rolohaun/SimpleCore/Mantis_Toolhead/Left_Duct.stl

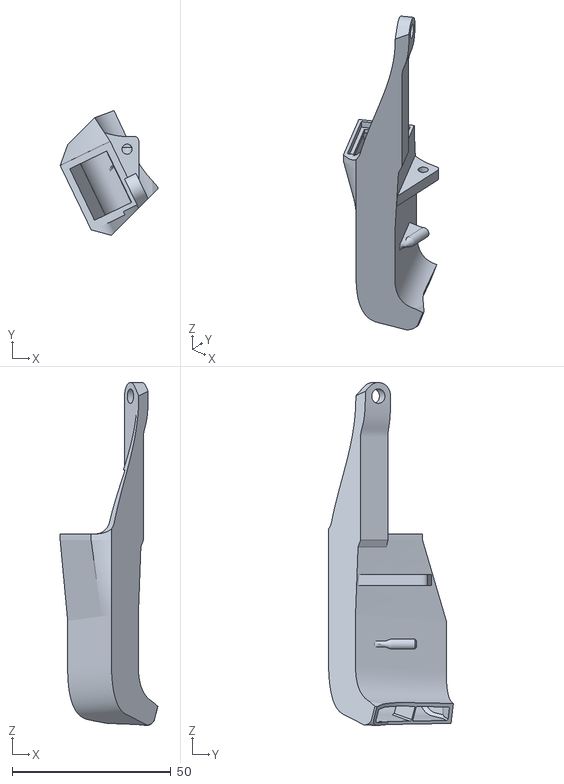
[picture p17: CAD file, 2022-10-22]
Mantis_Toolhead/Left_Duct.stl
30.8 x 39.3 x 108.1
