rolohaun/SimpleCore/Z/330mm Bed/1 x 330_Bed_Mount Left.stl

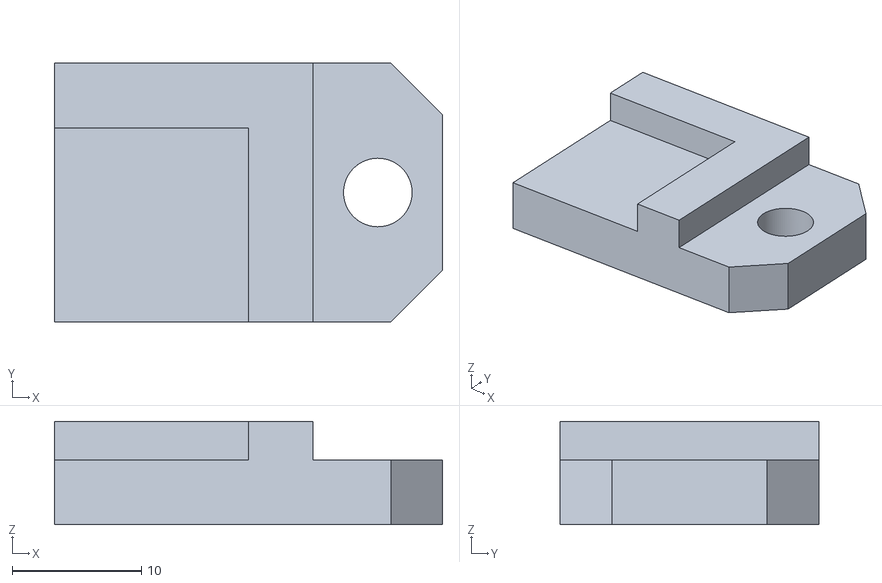
[picture p19: CAD file, 2022-05-16]
Z/330mm Bed/1 x 330_Bed_Mount Left.stl
30.0 x 20.0 x 8.00
