rolohaun/SimpleCore/Z/z_stepper_Mount_left.stl

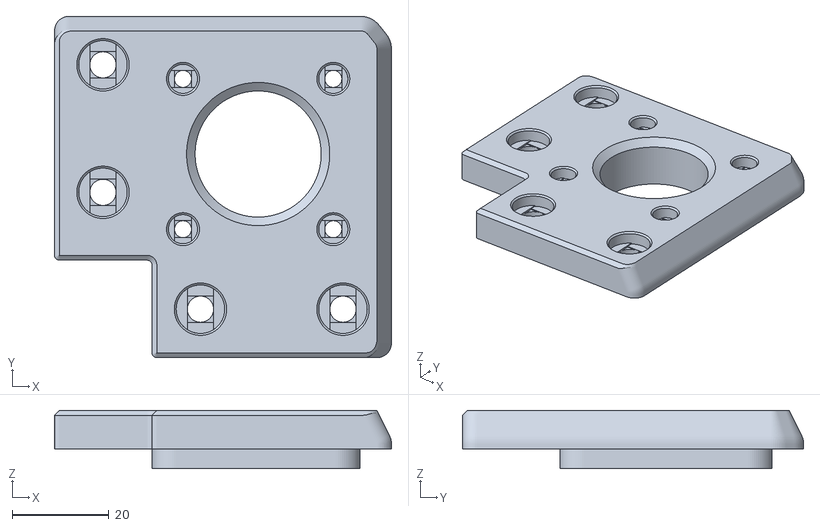
[picture p20: CAD file, 2022-10-22]
Z/z_stepper_Mount_left.stl
69.5 x 70.4 x 12.0
