rolohaun/SimpleCore/Frame/1 X B_Motor_Mount_MK1.stl

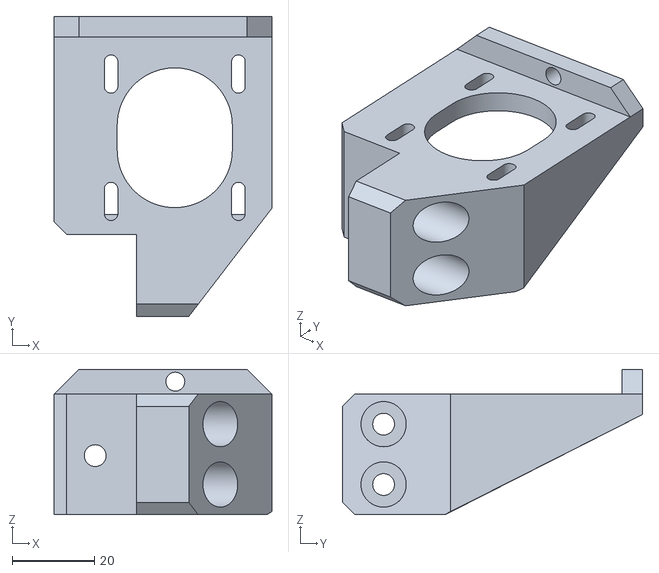
[picture p21: CAD file, 2022-10-22]
Frame/1 X B_Motor_Mount_MK1.stl
53.0 x 73.0 x 35.4
