rolohaun/SimpleCore/Mantis_Toolhead/X_hotend_mount_klicky.stl

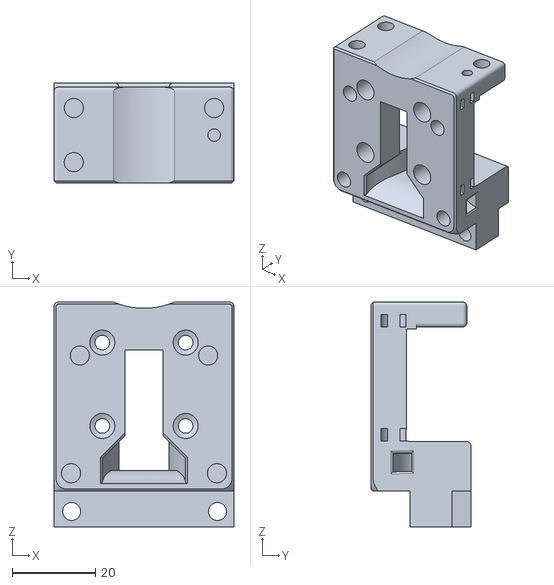
[picture p22: CAD file, 2022-10-22]
Mantis_Toolhead/X_hotend_mount_klicky.stl
43.2 x 24.0 x 54.0
