rolohaun/SimpleCore/Z/330mm Bed/3 X 300mm_Z_Ledge.stl

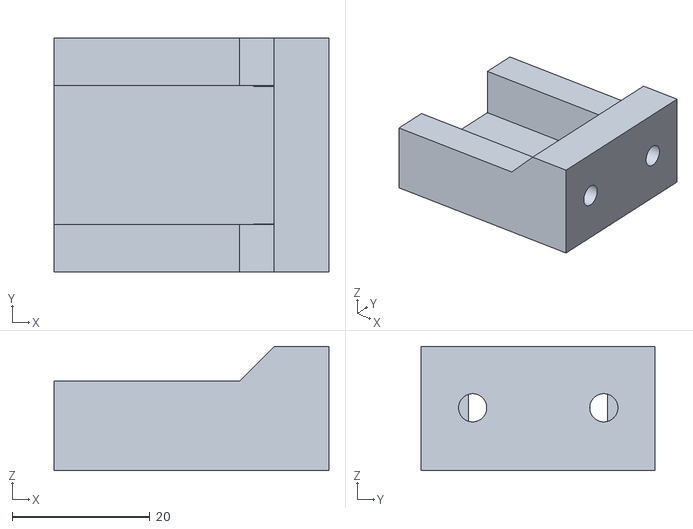
[picture p23: CAD file, 2022-05-16]
Z/330mm Bed/3 X 300mm_Z_Ledge.stl
40.0 x 34.0 x 18.1
