rolohaun/SimpleCore/Z/z_stepper_Mount_rear.stl

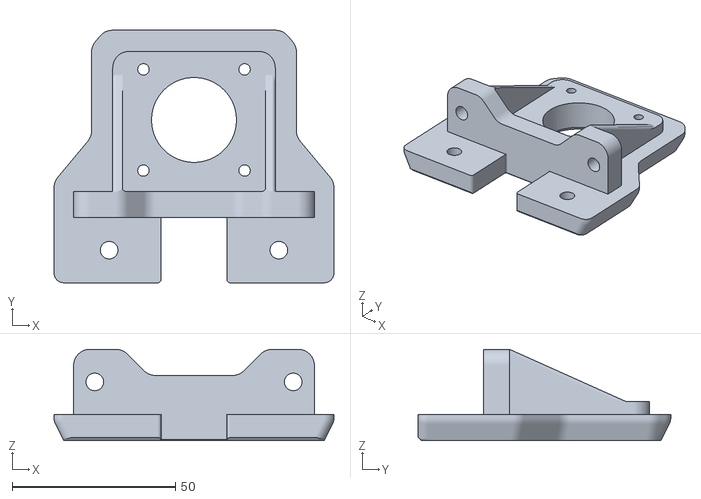
[picture p24: CAD file, 2022-10-22]
Z/z_stepper_Mount_rear.stl
85.8 x 77.4 x 28.0
