rolohaun/SimpleCore/Mantis_Toolhead/Dragon_mount_sherpa.stl

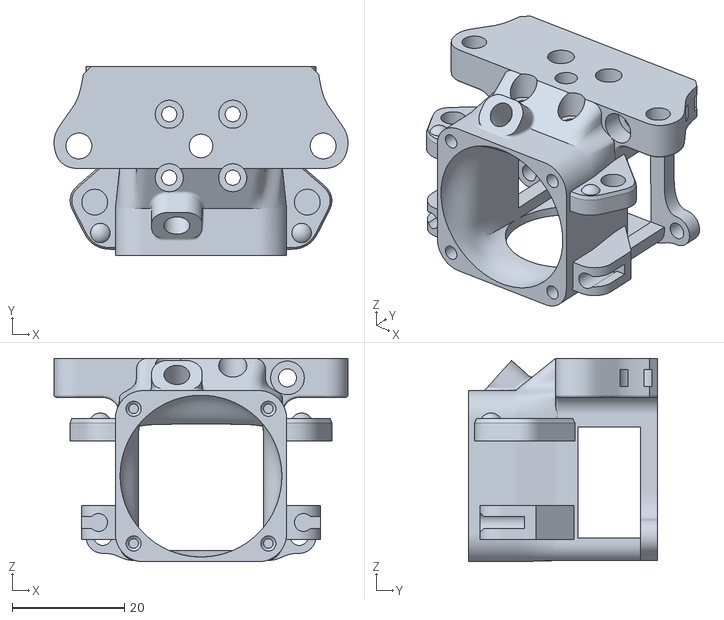
[picture p25: CAD file, 2022-10-22]
Mantis_Toolhead/Dragon_mount_sherpa.stl
52.4 x 33.7 x 36.2
