rolohaun/SimpleCore/User Mods/CF Tube X Axis guides/railgudie large opensided x2.stl

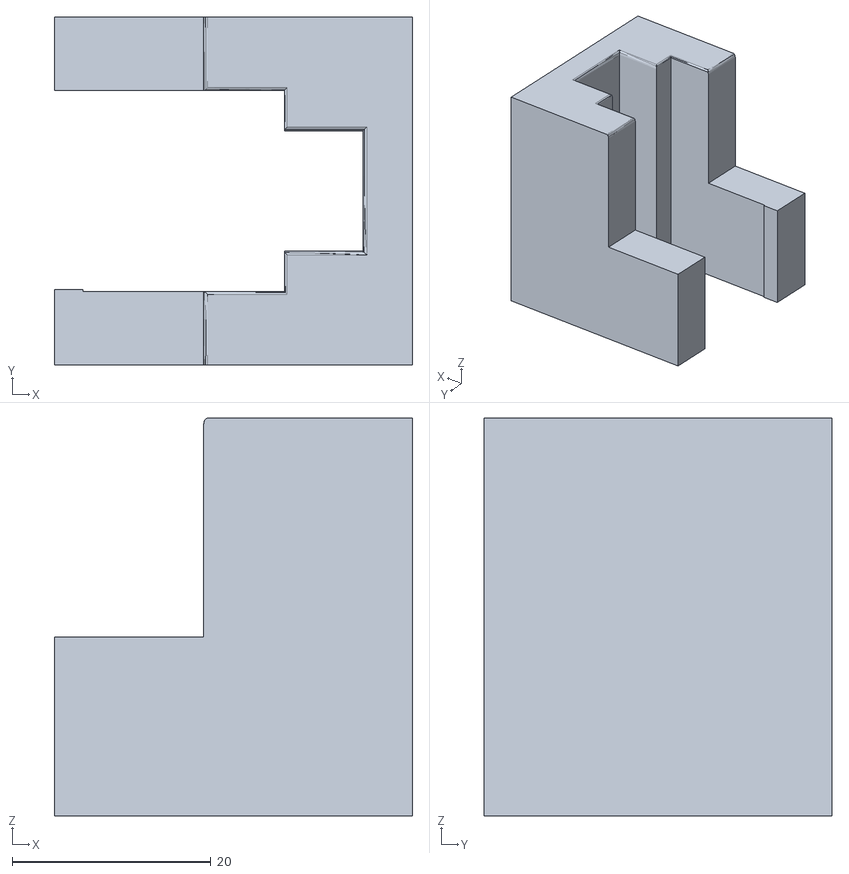
[picture p26: CAD file, 2022-08-15]
User Mods/CF Tube X Axis guides/railgudie large opensided x2.stl
36.0 x 35.0 x 40.0
