rolohaun/SimpleCore/Y/Left_Y_Carriage_Bottom.stl

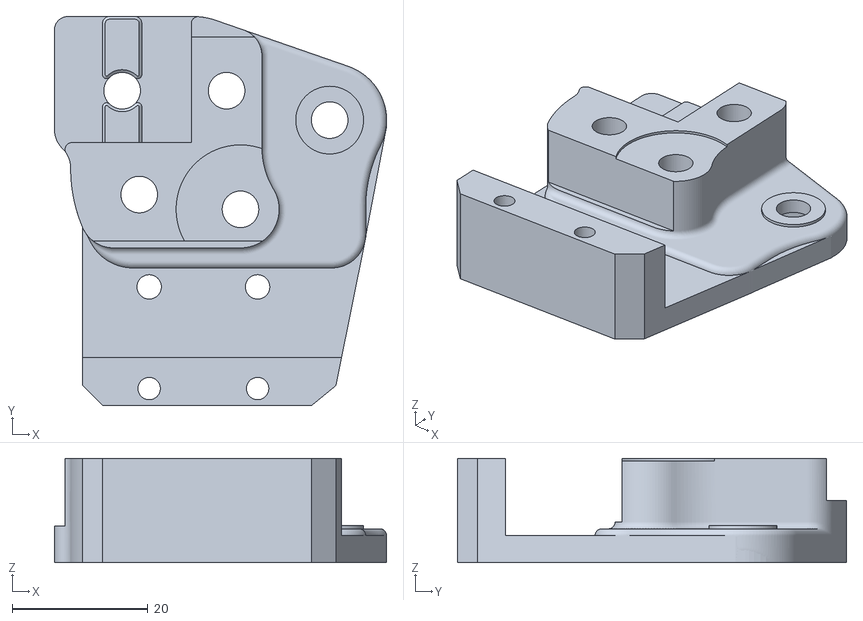
[picture p27: CAD file, 2022-10-22]
Y/Left_Y_Carriage_Bottom.stl
49.0 x 57.4 x 15.4
