rolohaun/SimpleCore/User Mods/CF Tube X Axis guides/Railguide narrow x2.stl

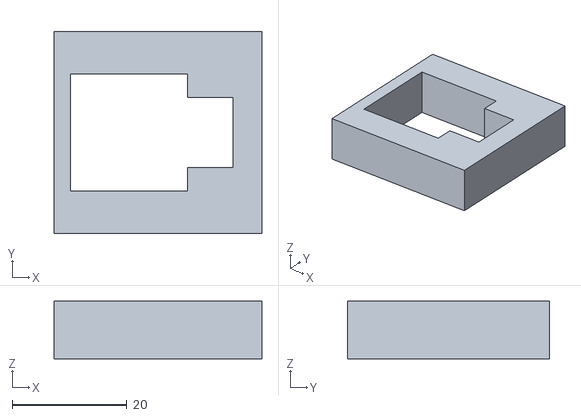
[picture p28: CAD file, 2022-08-15]
User Mods/CF Tube X Axis guides/Railguide narrow x2.stl
36.3 x 35.3 x 10.1
