rolohaun/SimpleCore/Z/Z_Bed_Mount_Rear.stl

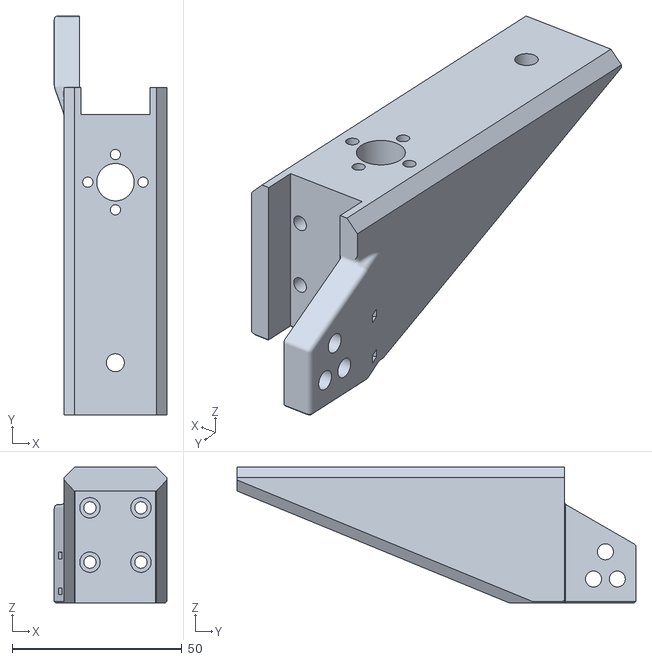
[picture p30: CAD file, 2022-10-22]
Z/Z_Bed_Mount_Rear.stl
33.1 x 117.4 x 39.9
