rolohaun/SimpleCore/Frame/Right_Idler_Mount.stl

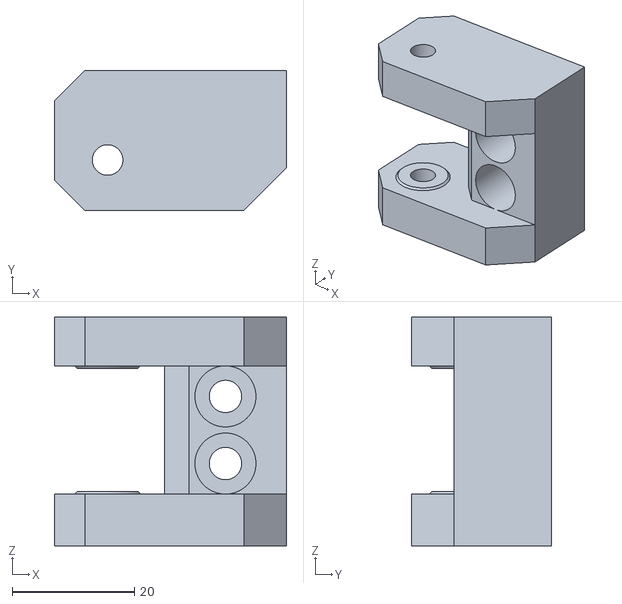
[picture p31: CAD file, 2022-10-22]
Frame/Right_Idler_Mount.stl
38.0 x 23.0 x 37.5
