rolohaun/SimpleCore/User Mods/CF Tube X Axis guides/2mm pilot hole guide optional.stl

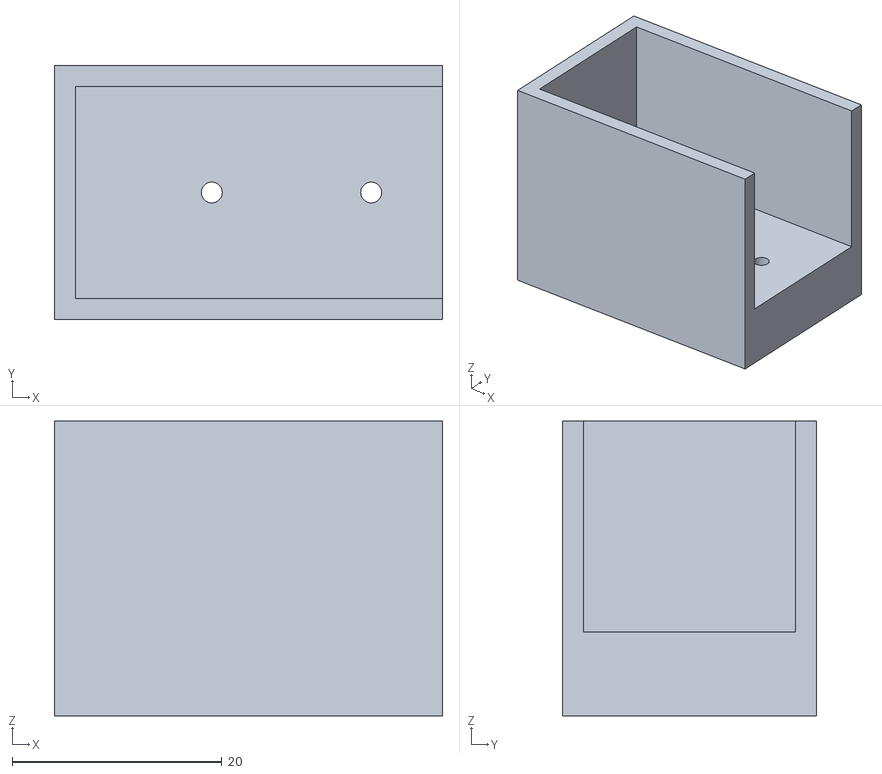
[picture p32: CAD file, 2022-08-15]
User Mods/CF Tube X Axis guides/2mm pilot hole guide optional.stl
37.0 x 24.2 x 28.1
