rolohaun/SimpleCore/Y/1 X Left_Y_Carriage_Top.stl

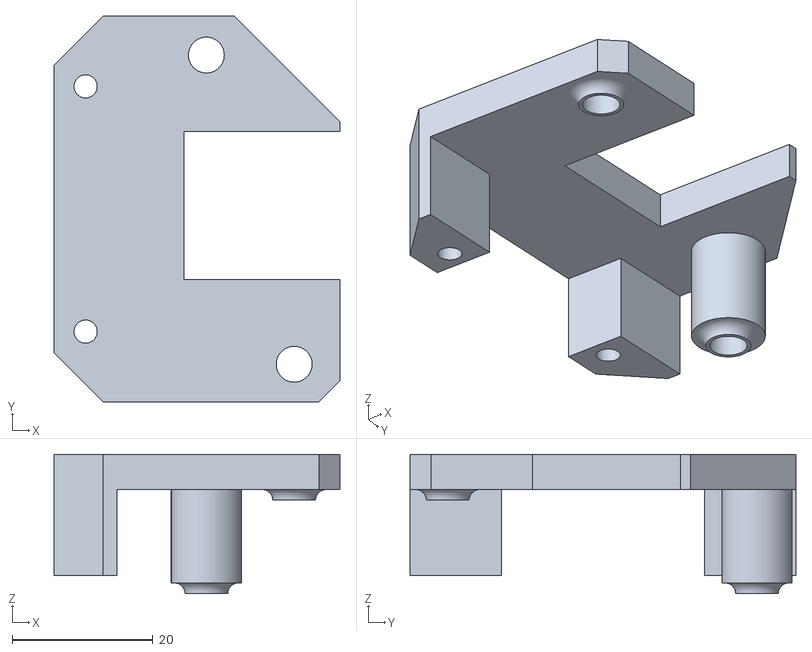
[picture p33: CAD file, 2022-03-20]
Y/1 X Left_Y_Carriage_Top.stl
40.7 x 54.9 x 19.8
