rolohaun/SimpleCore/Y/1 X Right_X_Endstop_slide.stl

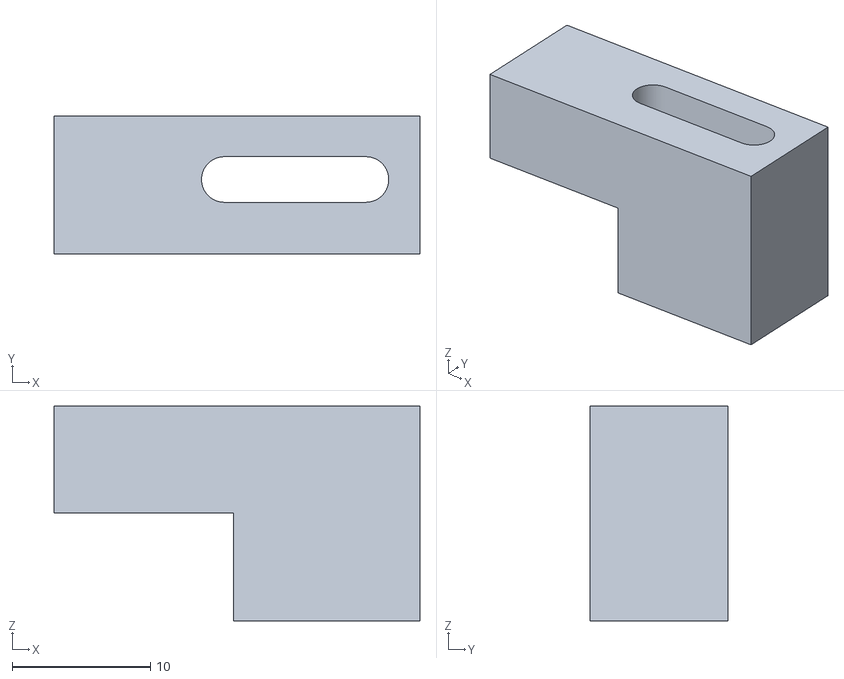
[picture p34: CAD file, 2022-03-20]
Y/1 X Right_X_Endstop_slide.stl
26.5 x 10.0 x 15.6
