rolohaun/SimpleCore/Z/1 X Z_Motor_Mount_Right_MK1.stl

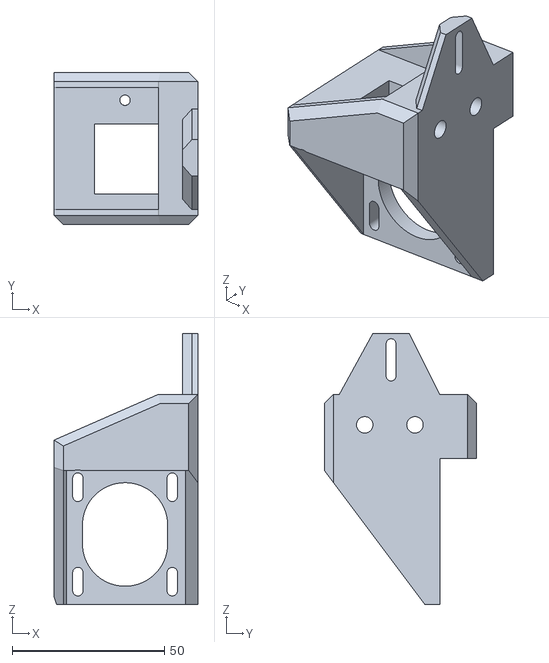
[picture p35: CAD file, 2022-08-24]
Z/1 X Z_Motor_Mount_Right_MK1.stl
47.2 x 50.0 x 89.0
