rolohaun/SimpleCore/Frame/spool_holder.stl

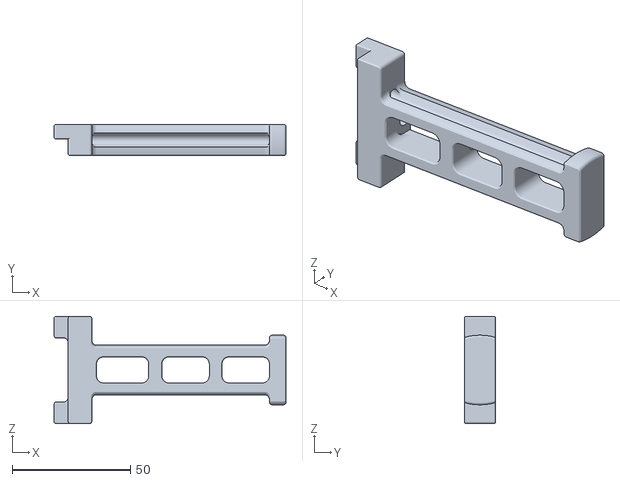
[picture p36: CAD file, 2022-10-22]
Frame/spool_holder.stl
98.0 x 13.0 x 45.4
