rolohaun/SimpleCore/Frame/bowen_retainer.stl

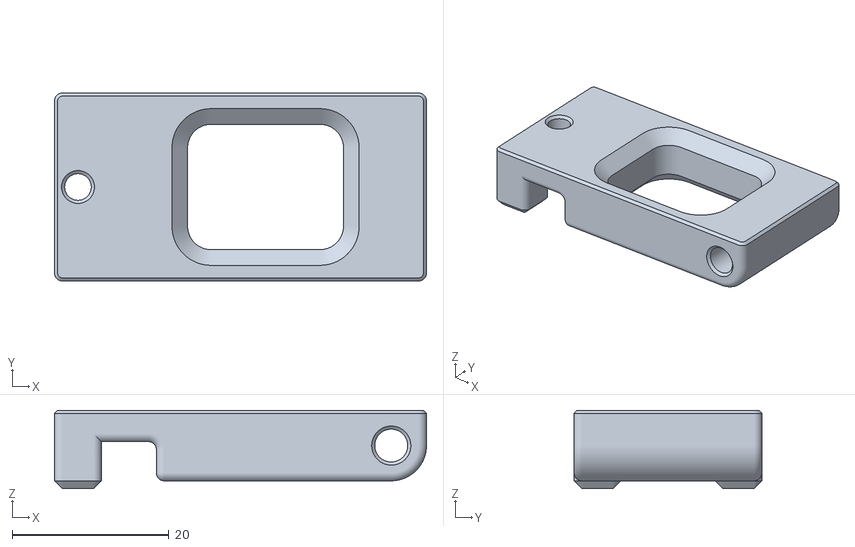
[picture p37: CAD file, 2022-10-22]
Frame/bowen_retainer.stl
47.5 x 24.0 x 10.00
