rolohaun/SimpleCore/Y/1 X Right_Y_Carriage_Bottom.stl

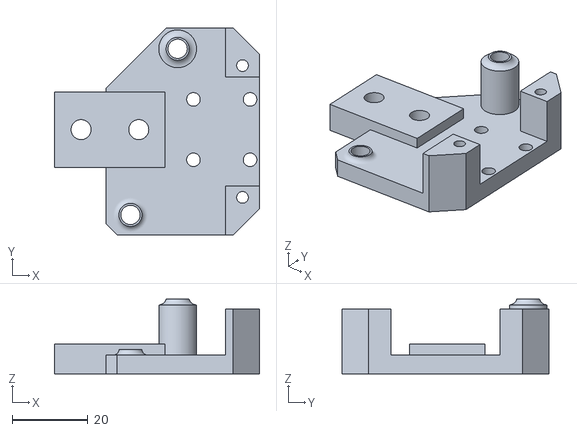
[picture p38: CAD file, 2022-03-20]
Y/1 X Right_Y_Carriage_Bottom.stl
54.3 x 54.9 x 19.8
