rolohaun/SimpleCore/Z/3 X Z_Bed_Mount_MG12H.stl

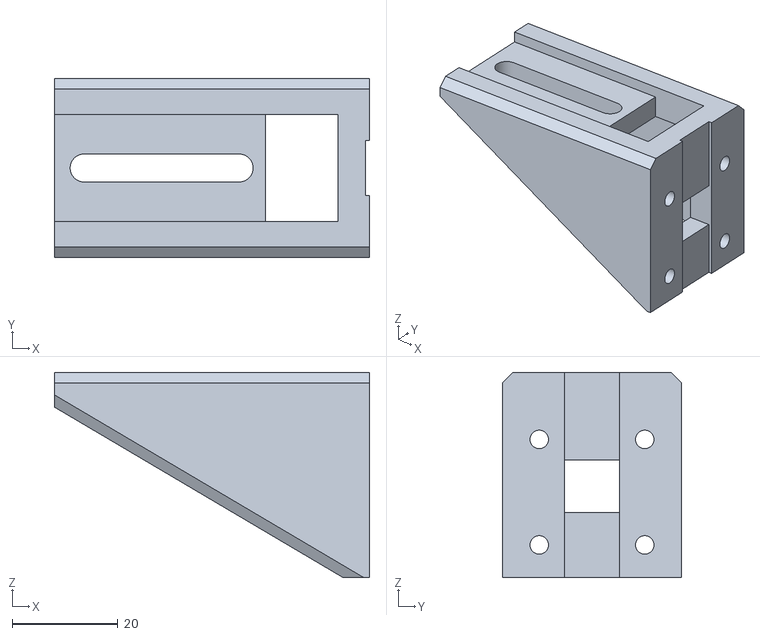
[picture p39: CAD file, 2022-08-22]
Z/3 X Z_Bed_Mount_MG12H.stl
59.7 x 34.0 x 38.9
