rolohaun/SimpleCore/Frame/Power_Inlet_Mount.stl

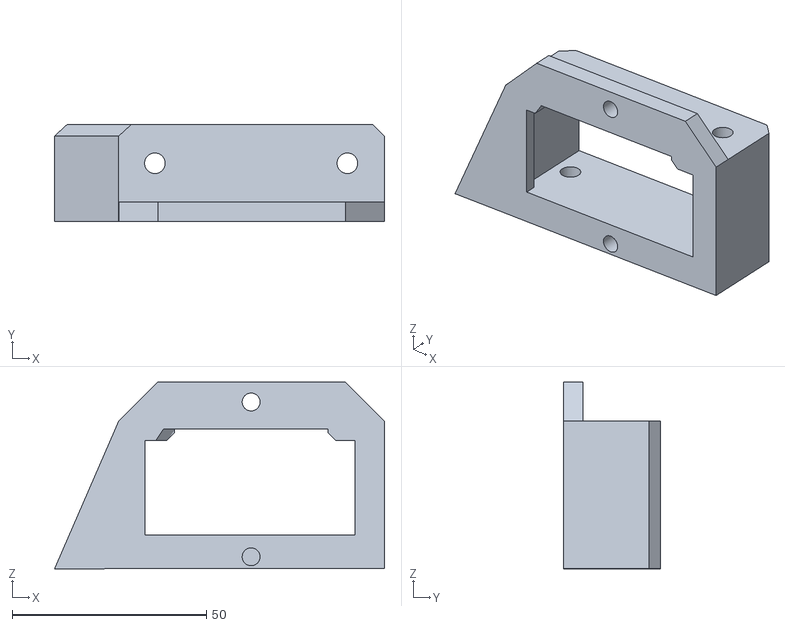
[picture p40: CAD file, 2022-10-10]
Frame/Power_Inlet_Mount.stl
84.8 x 25.0 x 48.0
