rolohaun/SimpleCore/Z/3 X Z_Linear_Rail_Top_Mount.stl

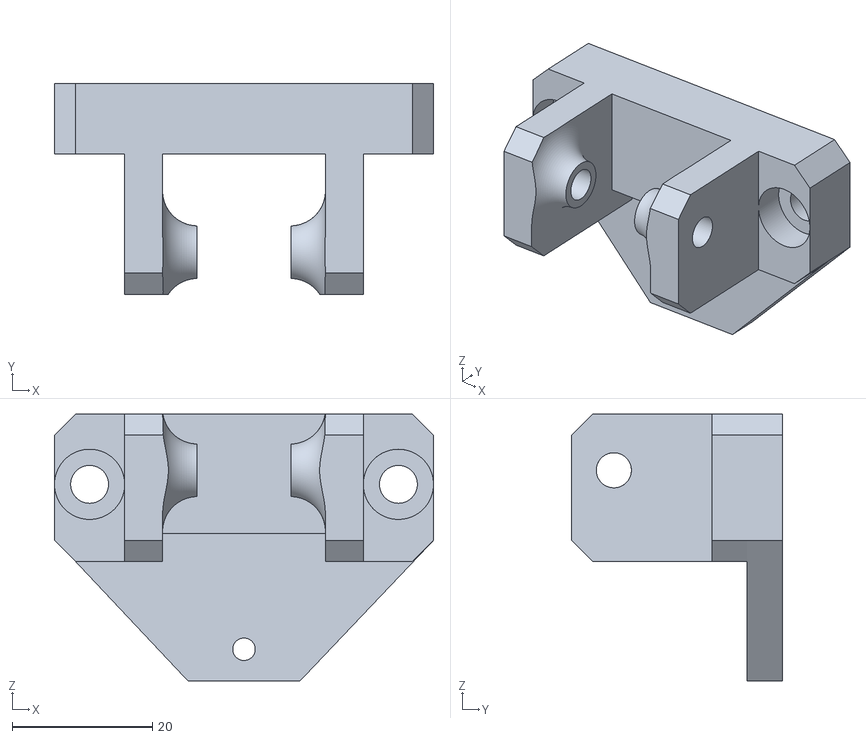
[picture p41: CAD file, 2022-05-29]
Z/3 X Z_Linear_Rail_Top_Mount.stl
54.0 x 30.0 x 38.0
