rolohaun/SimpleCore/Frame/Foot_Mount.stl

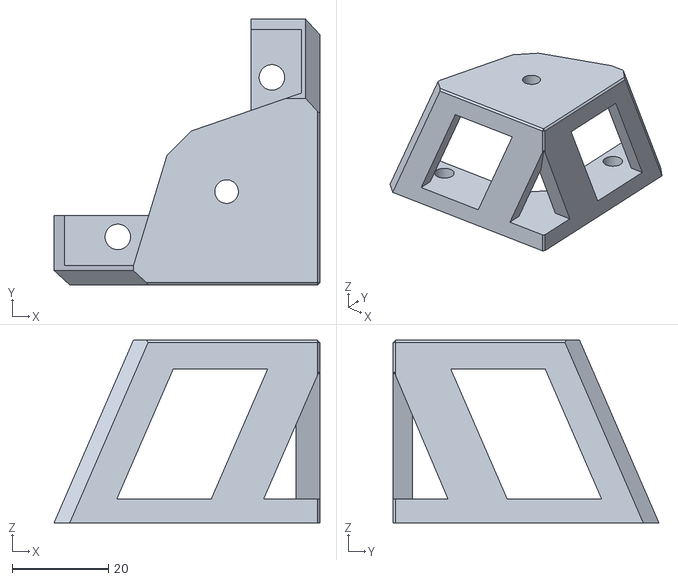
[picture p42: CAD file, 2022-10-10]
Frame/Foot_Mount.stl
55.3 x 55.3 x 38.0
