rolohaun/SimpleCore/Frame/Side_PSU_Mount.stl

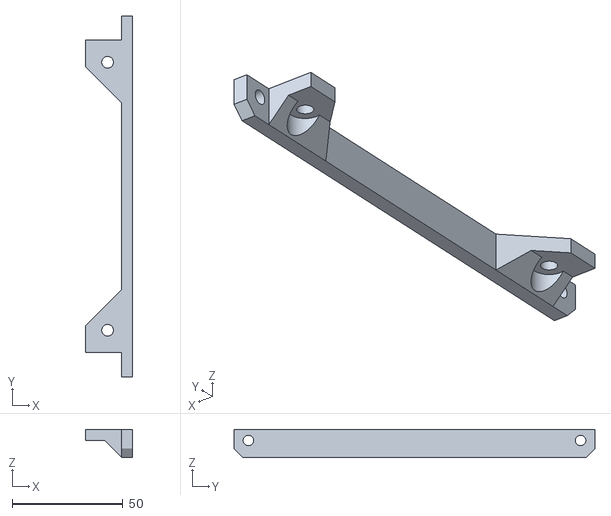
[picture p43: CAD file, 2022-10-10]
Frame/Side_PSU_Mount.stl
21.3 x 163.0 x 12.7
