rolohaun/SimpleCore/Frame/Rear_PSU_Mount.stl

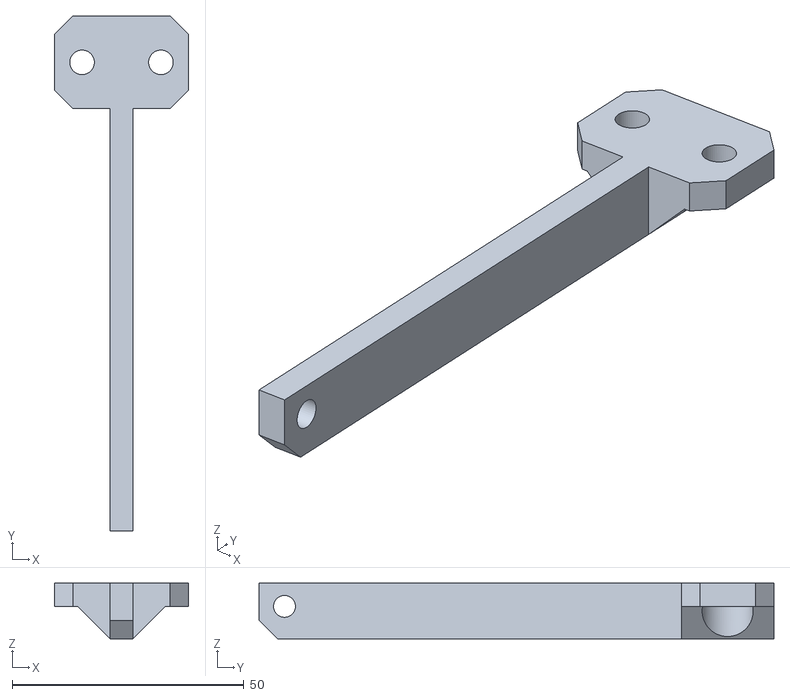
[picture p44: CAD file, 2022-10-10]
Frame/Rear_PSU_Mount.stl
29.0 x 111.1 x 12.0
