rolohaun/SimpleCore/Frame/1 X Power_Inlet.stl

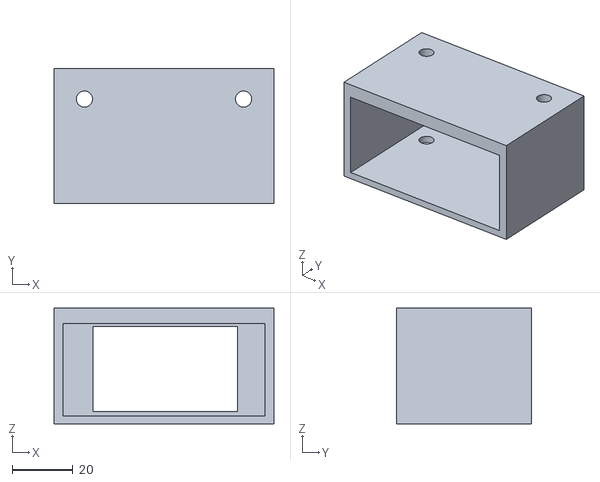
[picture p45: CAD file, 2022-07-22]
Frame/1 X Power_Inlet.stl
72.3 x 44.3 x 38.0
