rolohaun/SimpleCore/Frame/1 X Right_Idler_Mount.stl

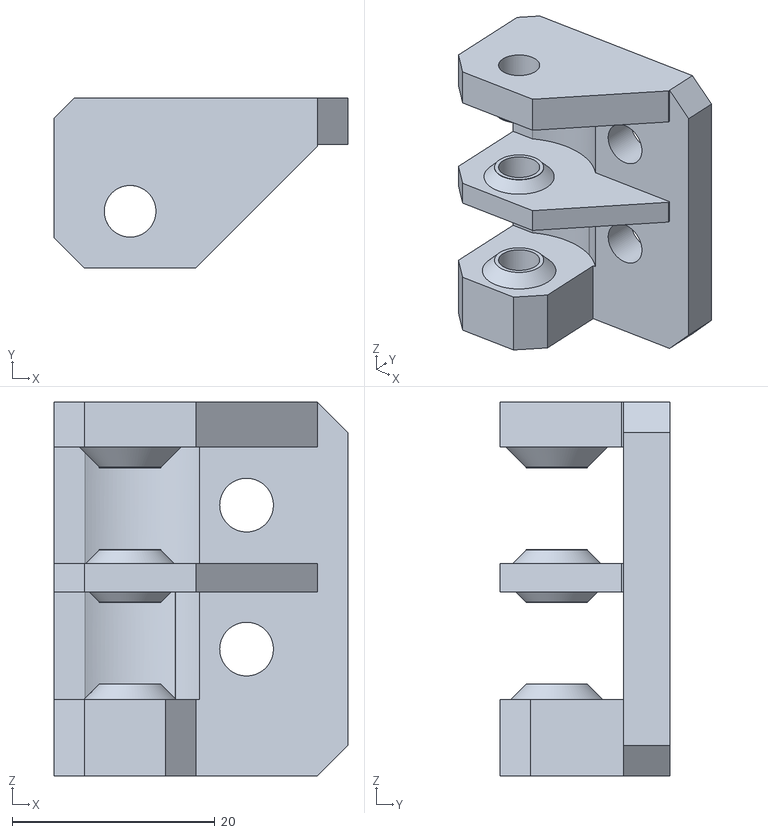
[picture p46: CAD file, 2022-07-12]
Frame/1 X Right_Idler_Mount.stl
29.0 x 16.8 x 36.9
