rolohaun/SimpleCore/Frame/1 X Front_PSU_Mount.stl

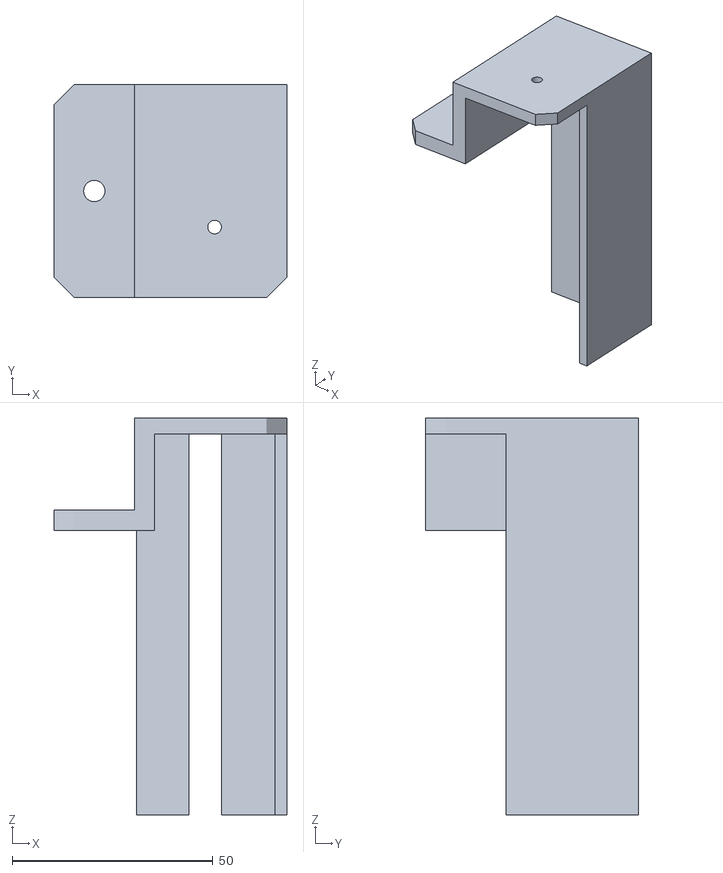
[picture p47: CAD file, 2022-03-31]
Frame/1 X Front_PSU_Mount.stl
58.0 x 53.0 x 99.0
