rolohaun/SimpleCore/Frame/4 X Foot_Mount.stl

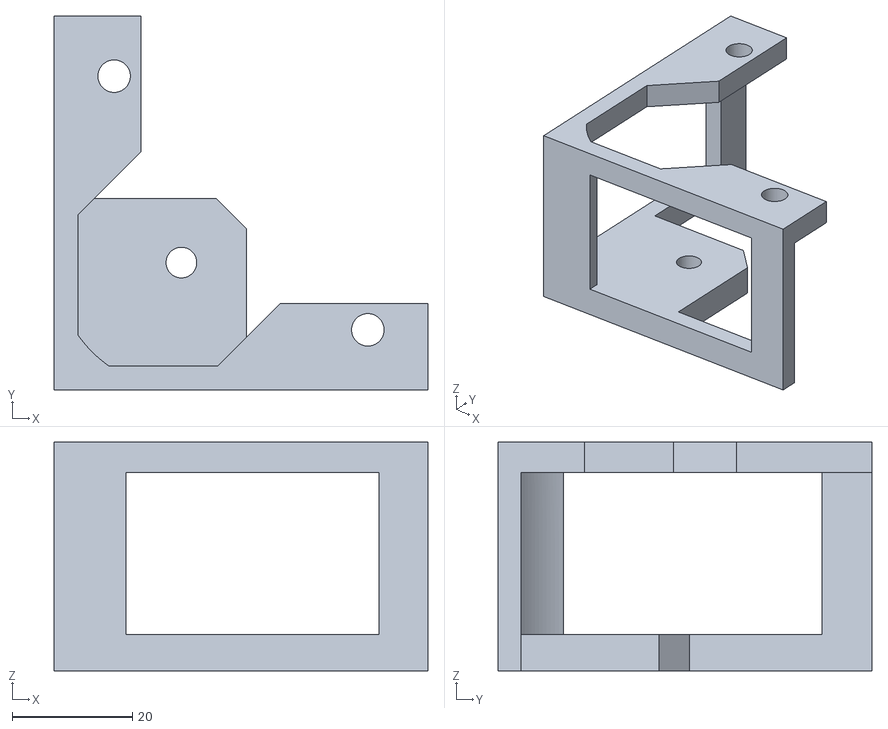
[picture p48: CAD file, 2022-03-20]
Frame/4 X Foot_Mount.stl
62.2 x 62.2 x 38.0
