rolohaun/SimpleCore/Frame/Guide_Tube_Mount.stl

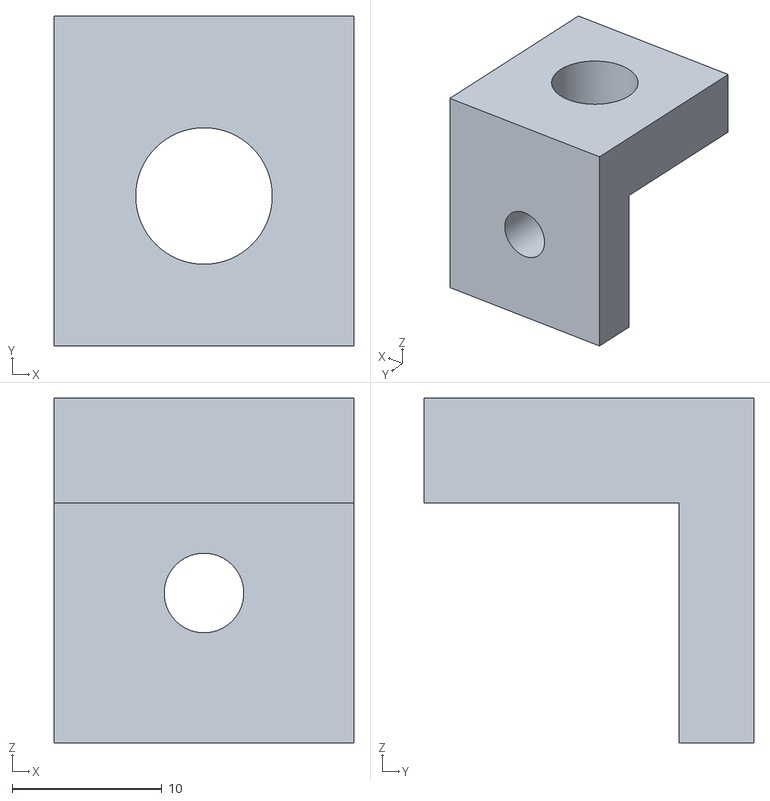
[picture p49: CAD file, 2022-03-20]
Frame/Guide_Tube_Mount.stl
20.0 x 22.0 x 23.0
