rolohaun/SimpleCore/Build_Photos/20221109_170549.jpg

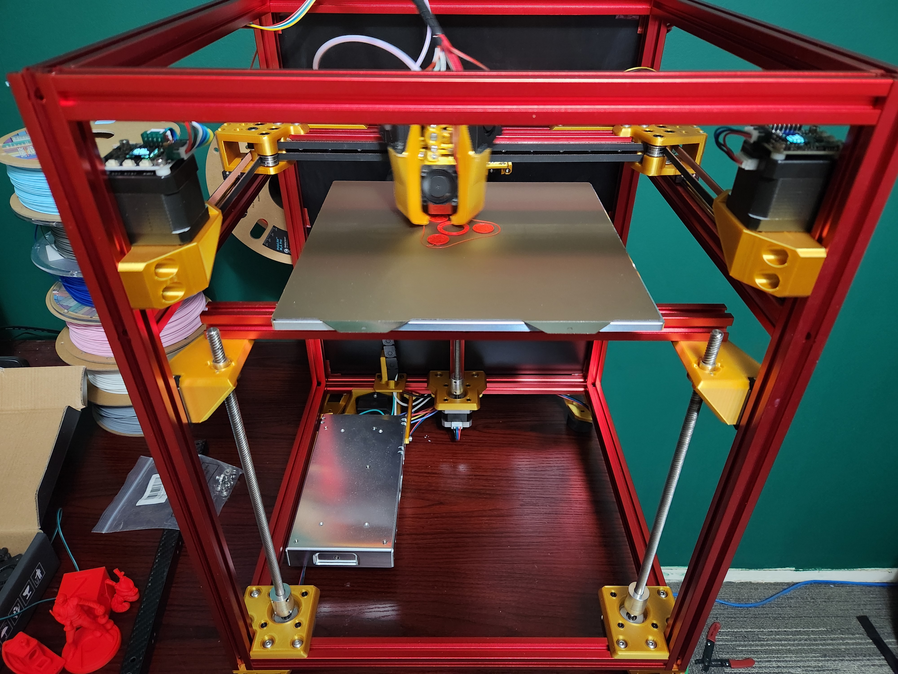
Build_Photos/20221109_170549.jpg
