rolohaun/SimpleCore/Build_Photos/20221109_211727.jpg

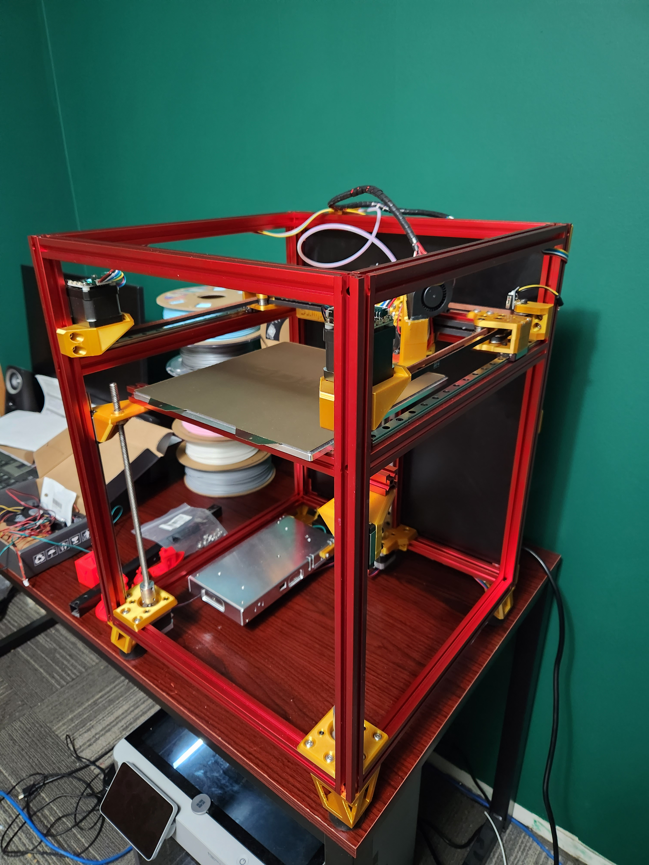
Build_Photos/20221109_211727.jpg
