rolohaun/SimpleCore/Build_Photos/20221109_211737.jpg

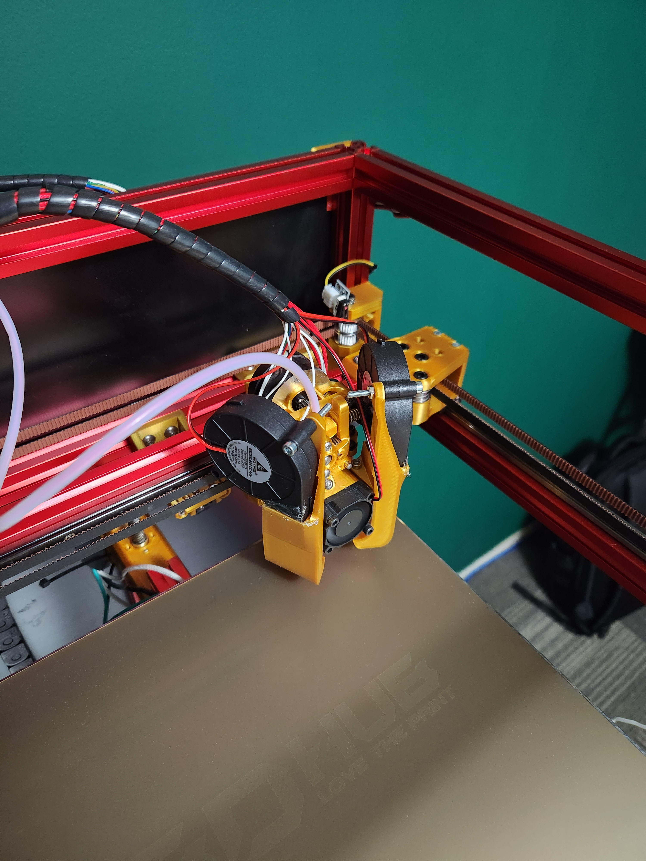
Build_Photos/20221109_211737.jpg
