rolohaun/SimpleCore/Build_Photos/Idler_Mount.jpg

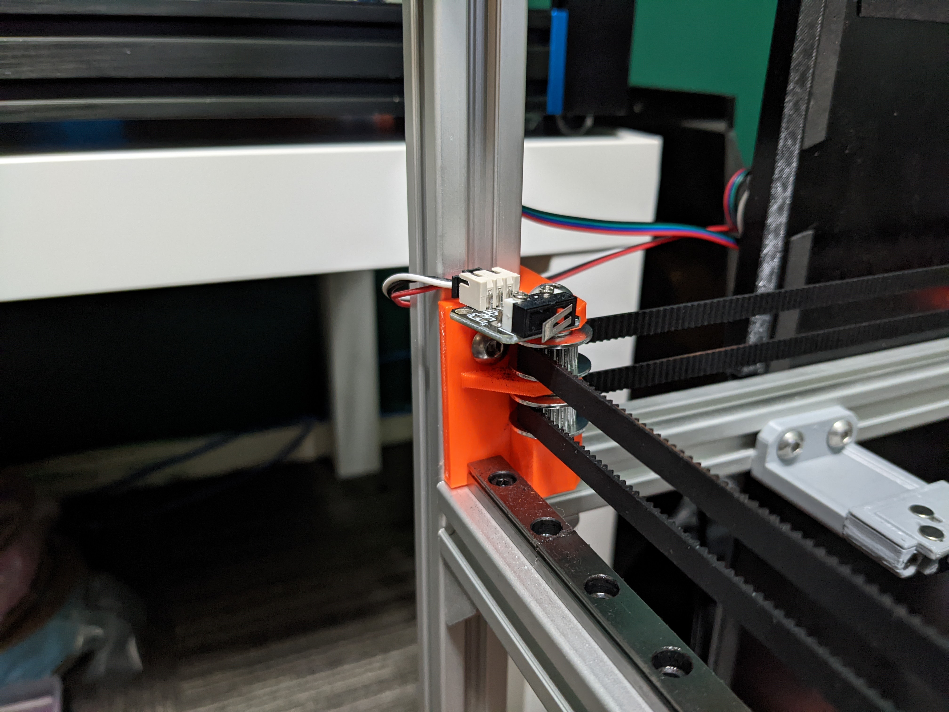
Build_Photos/Idler_Mount.jpg
