rolohaun/SimpleCore/Build_Photos/Rear_Z_Mount.jpg

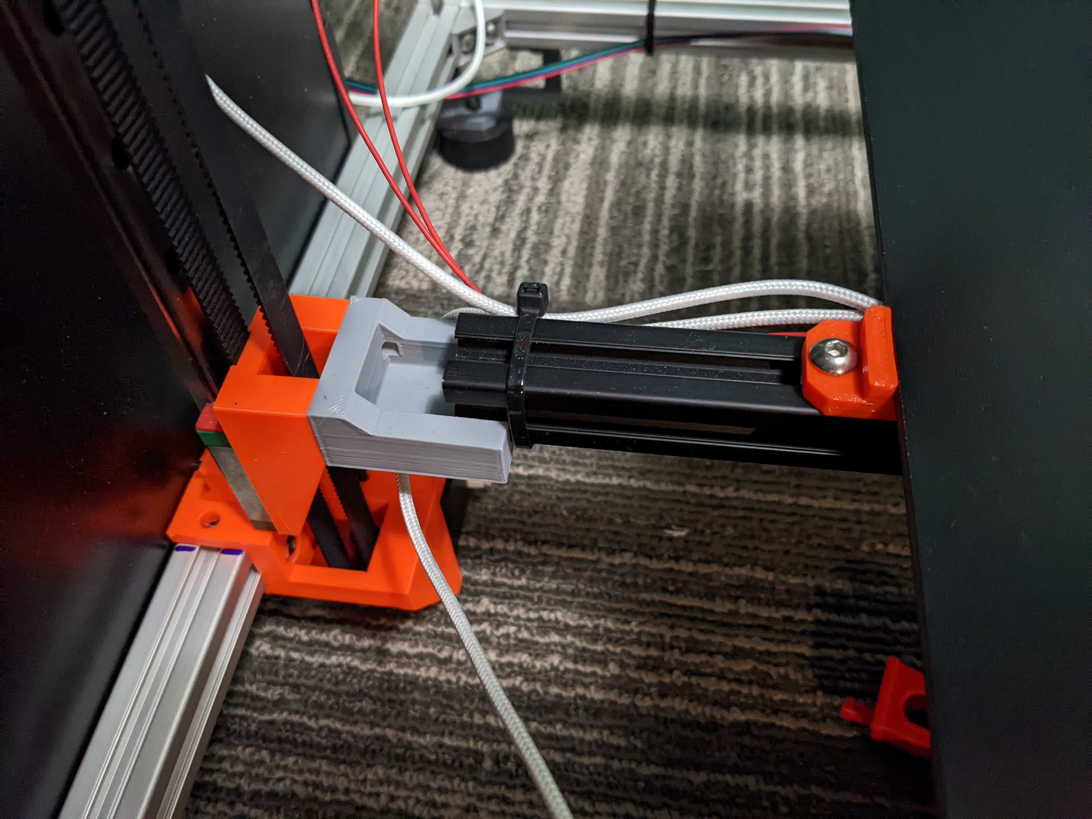
Build_Photos/Rear_Z_Mount.jpg
