rolohaun/SimpleCore/Build_Photos/Z motor mount.jpg

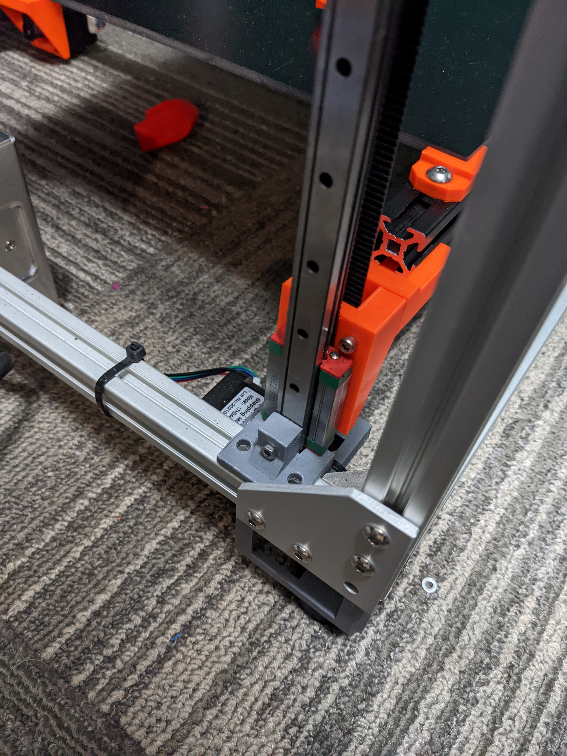
Build_Photos/Z motor mount.jpg
